dvorak55/dombrick45/image-ver1/bg18.jpg

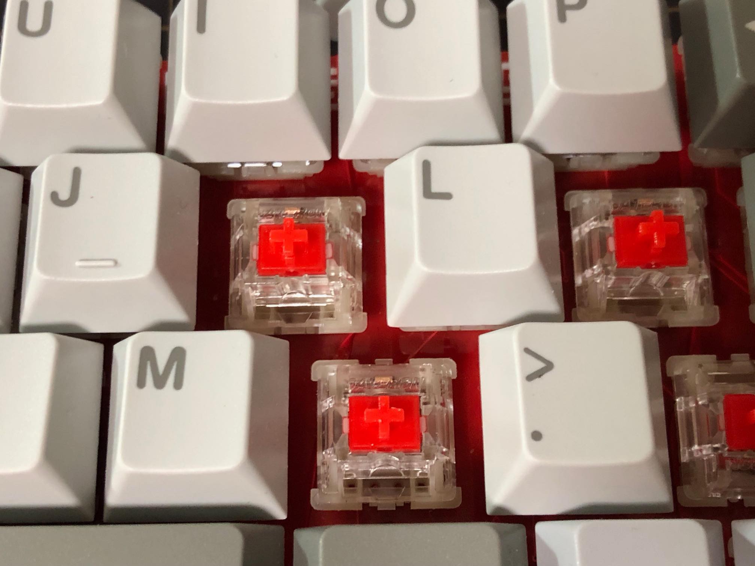
image-ver1/bg18.jpg
