dvorak55/dombrick45/image-ver1/bg20.jpg

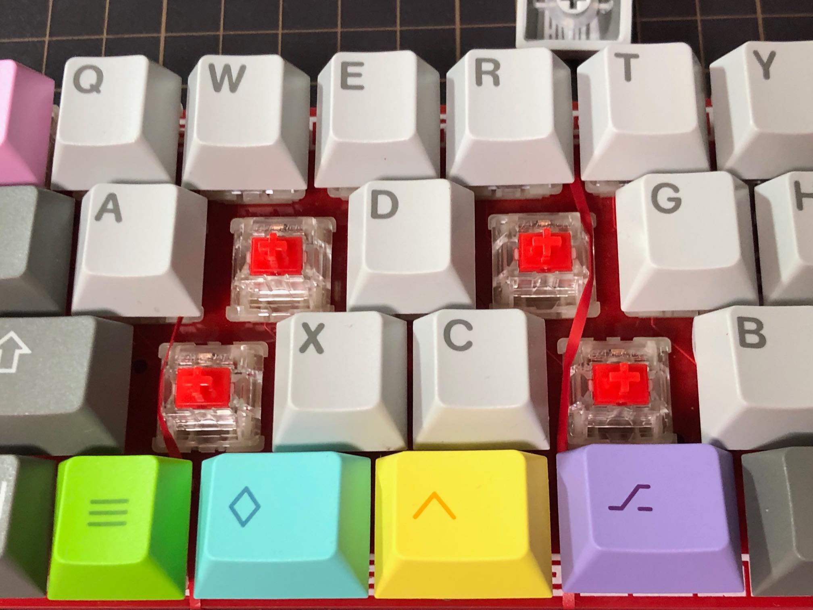
image-ver1/bg20.jpg
