dvorak55/dombrick45/image-ver1/bg22.jpg

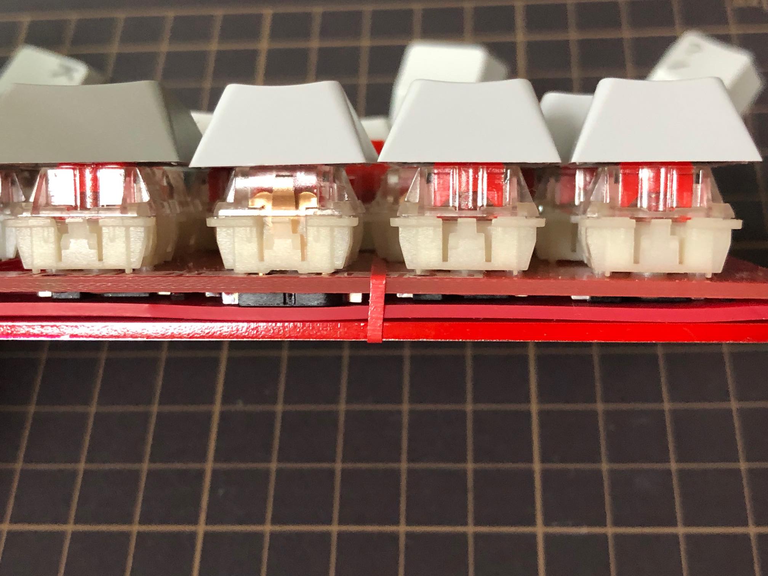
image-ver1/bg22.jpg
