dvorak55/dombrick45/image-ver1/bg23.jpg

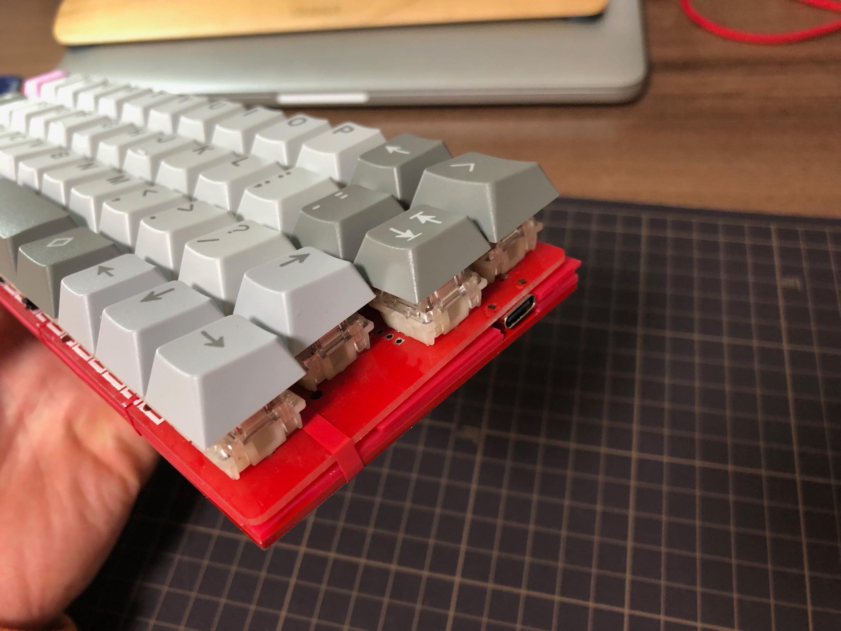
image-ver1/bg23.jpg
