dvorak55/dombrick45/keylayout/endgame-dvorak5.png

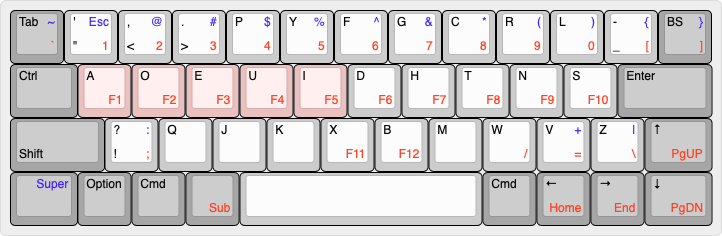
keylayout/endgame-dvorak5.png
