dvorak55/dombrick45/keylayout/endgame-dvorak6.png

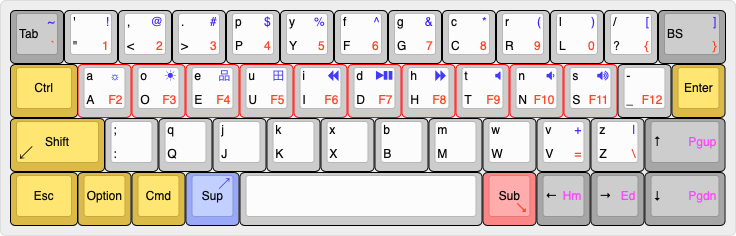
keylayout/endgame-dvorak6.png
