dvorak55/dombrick45/keylayout/endgame-dvorak7-1.png

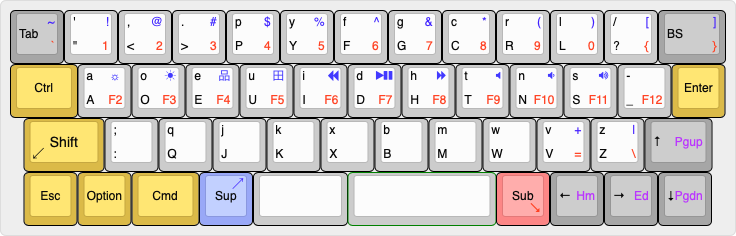
keylayout/endgame-dvorak7-1.png
