dvorak55/dombrick45/keylayout/endgame-dvorak8.png

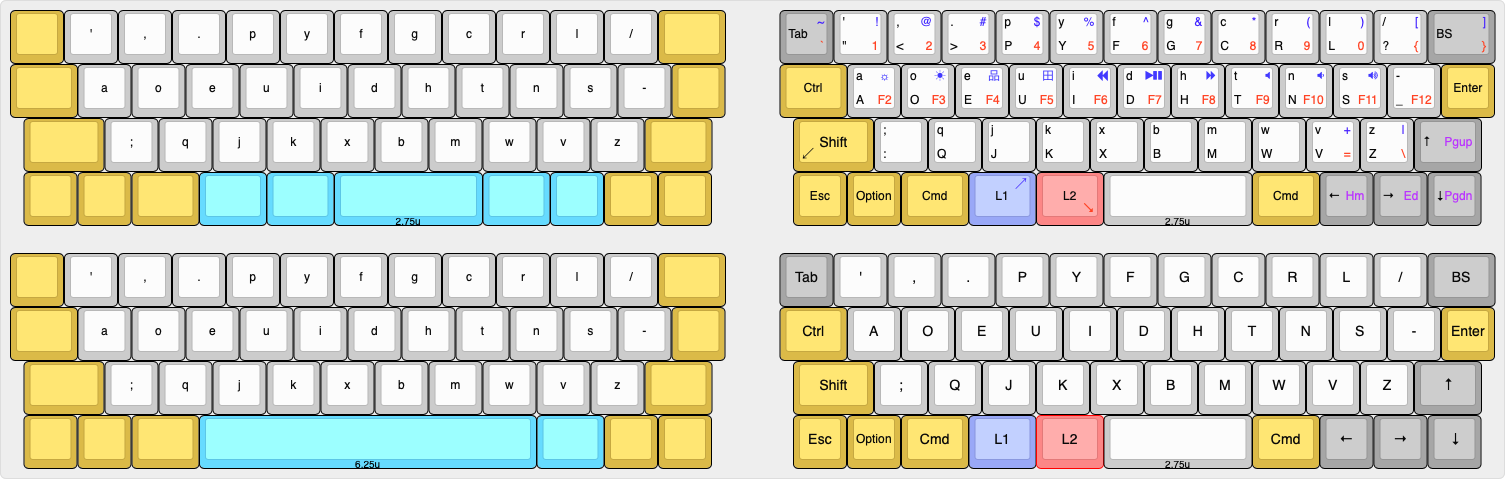
keylayout/endgame-dvorak8.png
