dvorak55/dombrick45/keylayout/endgame-dvorak9-3.png

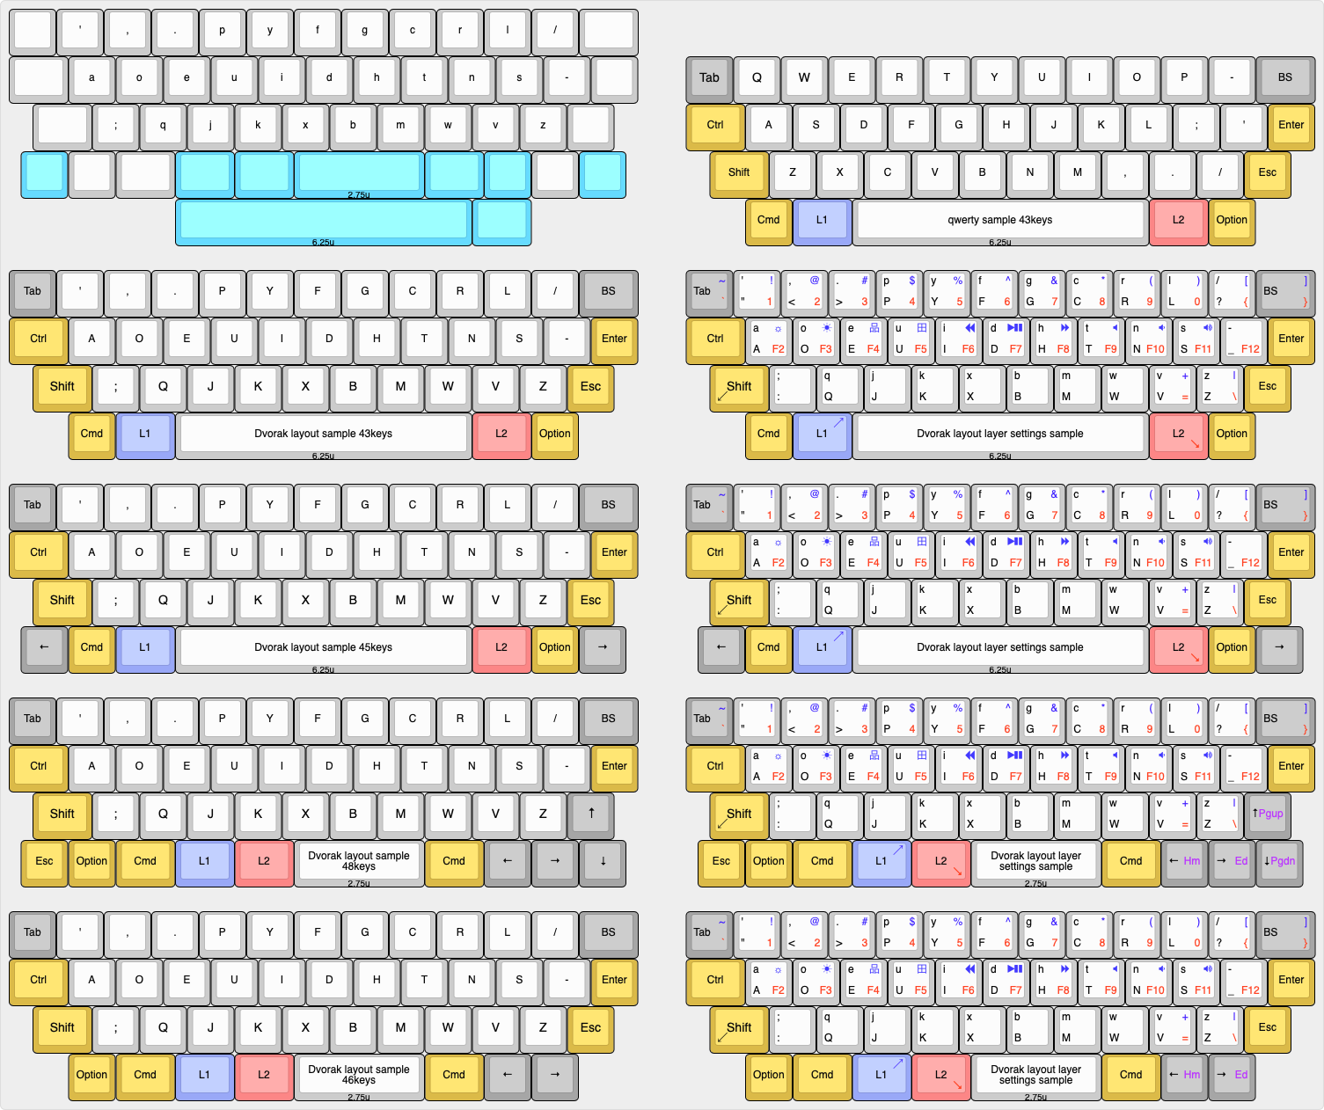
keylayout/endgame-dvorak9-3.png
