dvorak55/dombrick45/keylayout/endgame-dvorak10-1.png

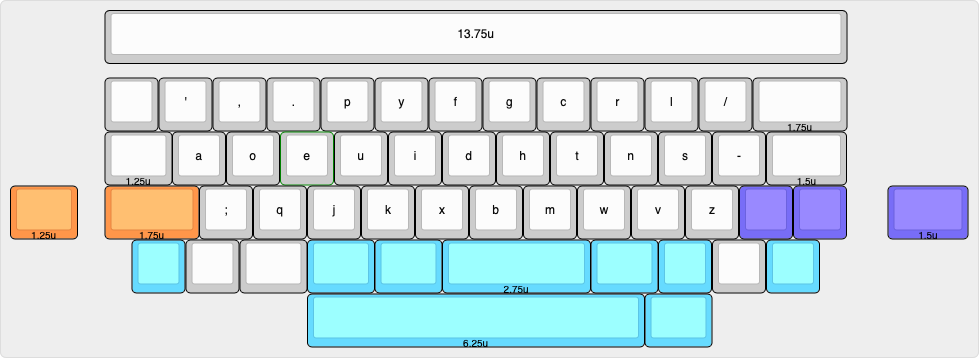
keylayout/endgame-dvorak10-1.png
