dvorak55/dombrick45/keylayout/endgame-dvorak10-2.png

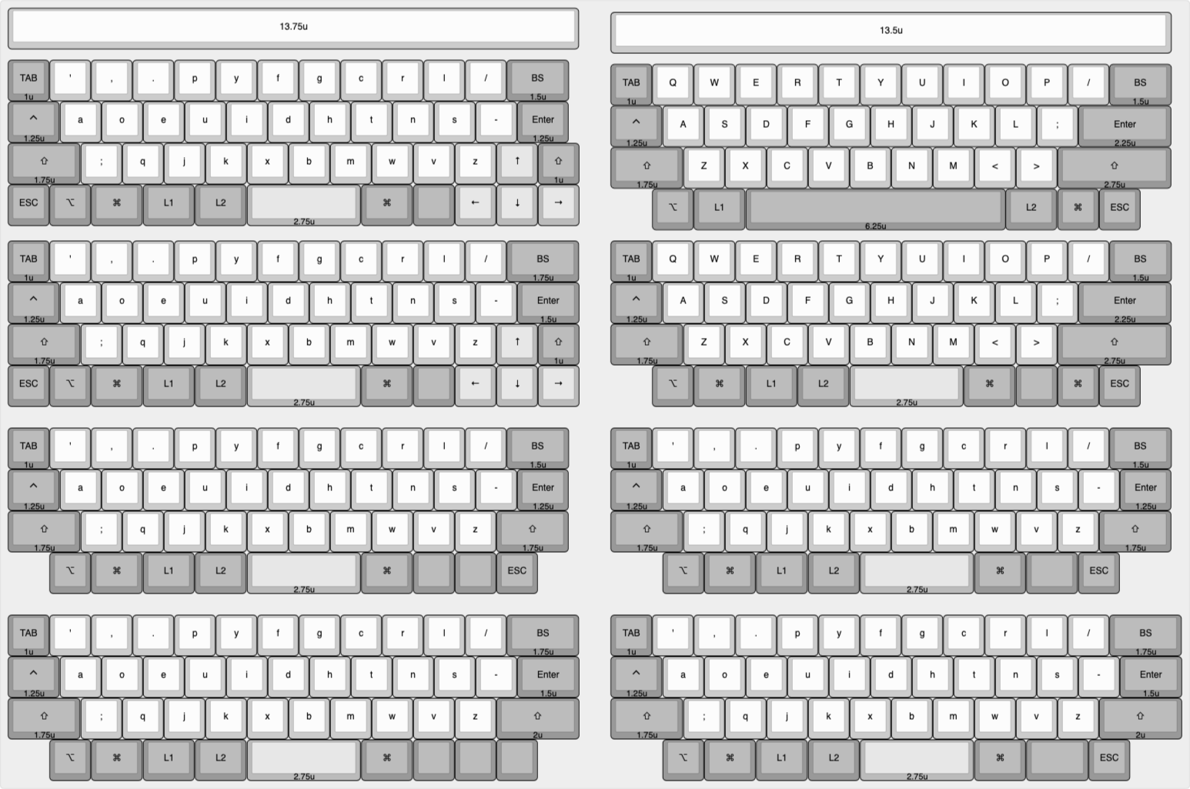
keylayout/endgame-dvorak10-2.png
