dvorak55/dombrick45/keylayout/endgame-dvorak10-3.png

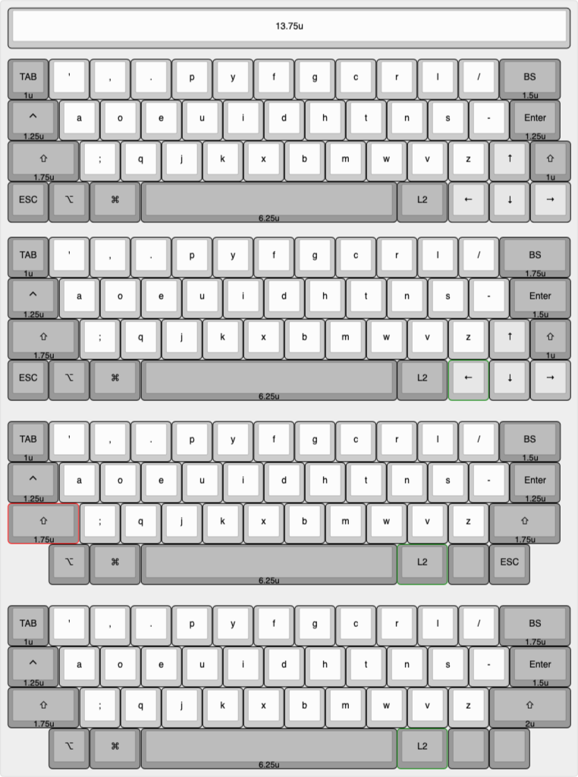
keylayout/endgame-dvorak10-3.png
