dvorak55/dombrick45/keylayout/endgame-dvorak11-2.png

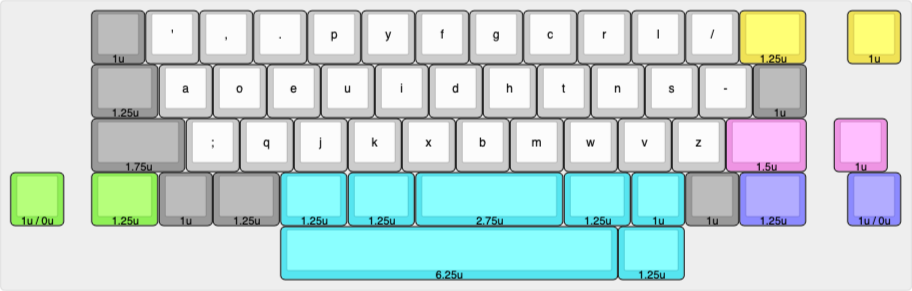
keylayout/endgame-dvorak11-2.png
