dvorak55/dombrick45/keylayout/endgame-dvorak11-3.png

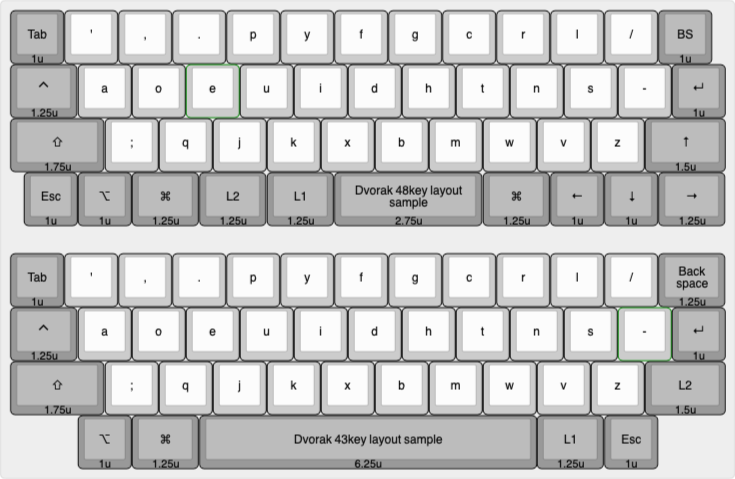
keylayout/endgame-dvorak11-3.png
