dvorak55/dombrick45/keylayout/endgame-dvorak12-2.png

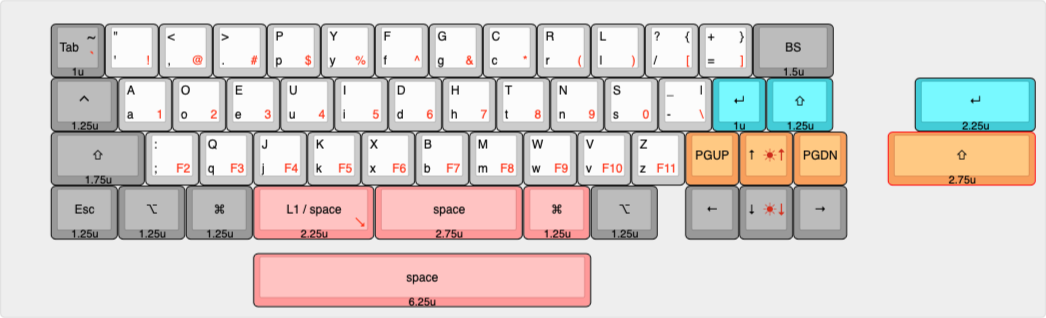
keylayout/endgame-dvorak12-2.png
