dvorak55/dombrick45/keylayout/endgame-dvorak12-3.png

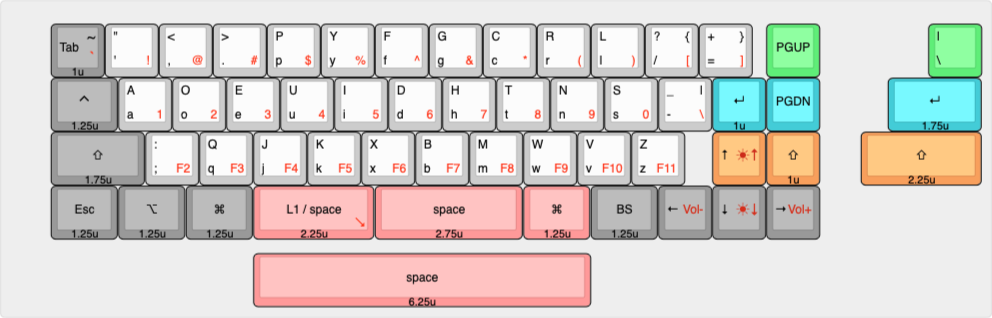
keylayout/endgame-dvorak12-3.png
