dvorak55/dombrick45/keylayout/endgame-dvorak12-4.png

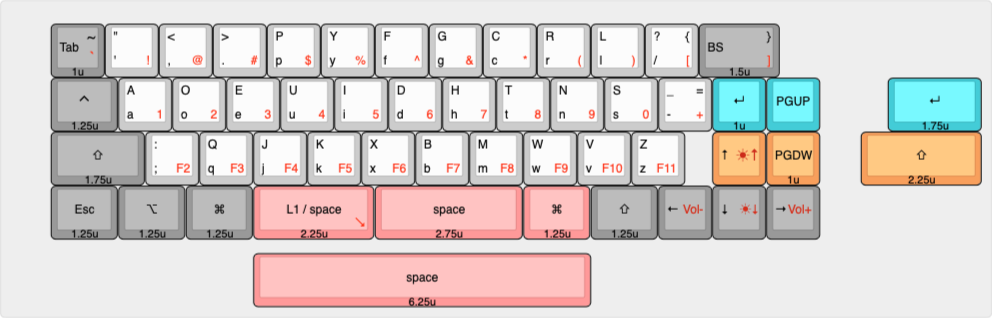
keylayout/endgame-dvorak12-4.png
