dvorak55/dombrick45/keylayout/endgame-dvorak13-1.png

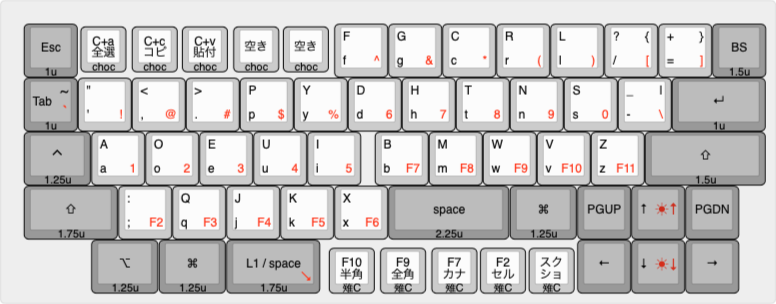
keylayout/endgame-dvorak13-1.png
