dvorak55/dombrick45/keylayout/risouno-dvorak49.png

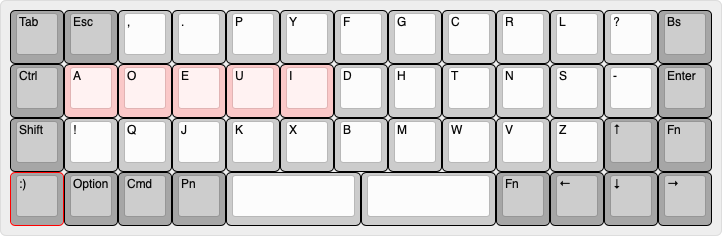
keylayout/risouno-dvorak49.png
