dvorak55/dombrick45/keylayout/ultimate-dombrick1.png

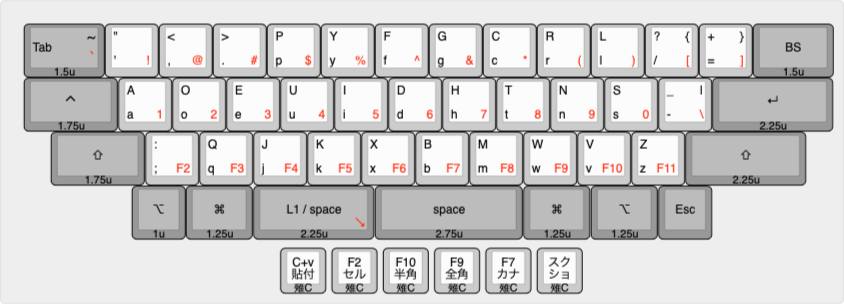
keylayout/ultimate-dombrick1.png
