dvorak55/dombrick45/qmk/keymaps/default/default-layout.png

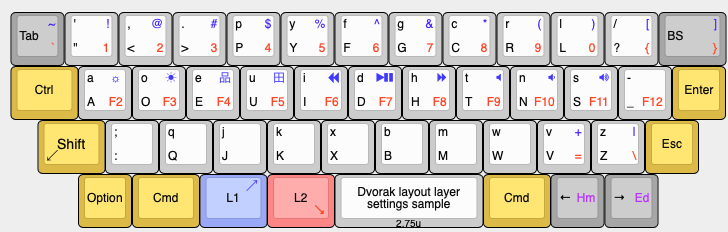
qmk/keymaps/default/default-layout.png
